qppd/smart-road-alert/ml/results/runs/detect/val/val_batch1_pred.jpg

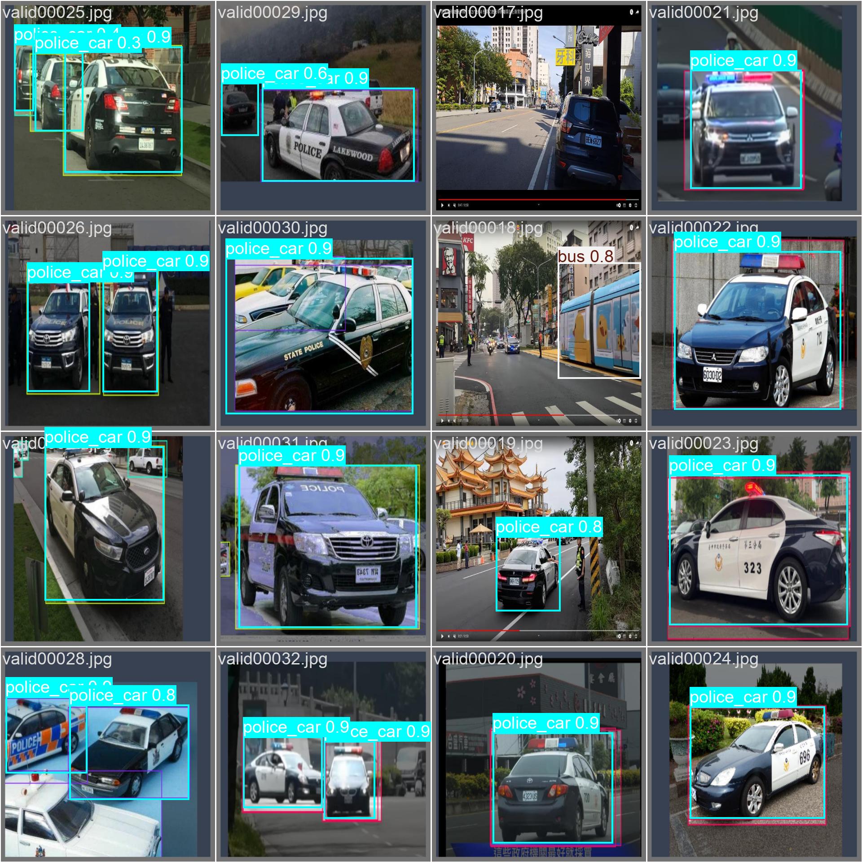
ml/results/runs/detect/val/val_batch1_pred.jpg
