qppd/smart-road-alert/ml/results/thesis_v3_results/g17_v3_final/val_batch2_pred.jpg

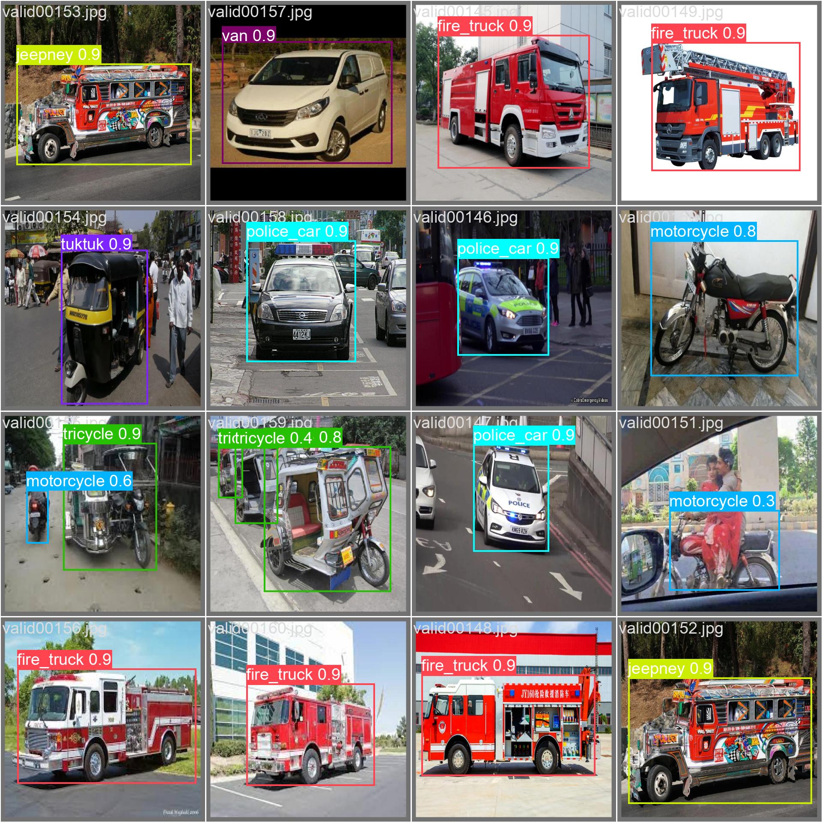
ml/results/thesis_v3_results/g17_v3_final/val_batch2_pred.jpg
