qppd/smart-road-alert/src/rpi/SmartRoadAlertHost/images/ambulance.jpg

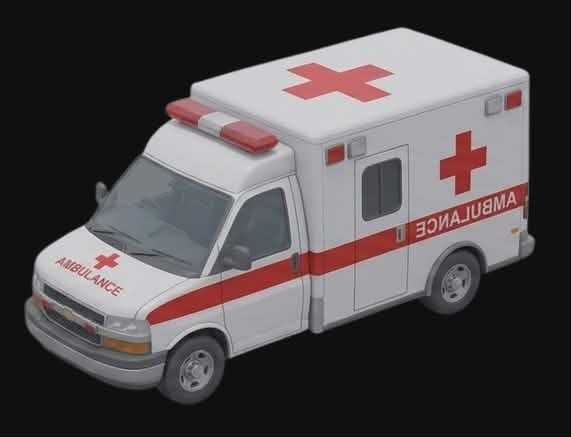
src/rpi/SmartRoadAlertHost/images/ambulance.jpg
