qppd/smart-road-alert/src/rpi/SmartRoadAlertHost/images/car.jpg

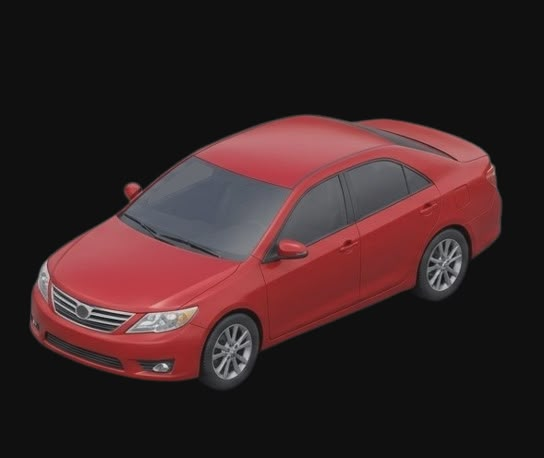
src/rpi/SmartRoadAlertHost/images/car.jpg
