qppd/smart-road-alert/src/rpi/SmartRoadAlertHost/images/ev_small.jpg

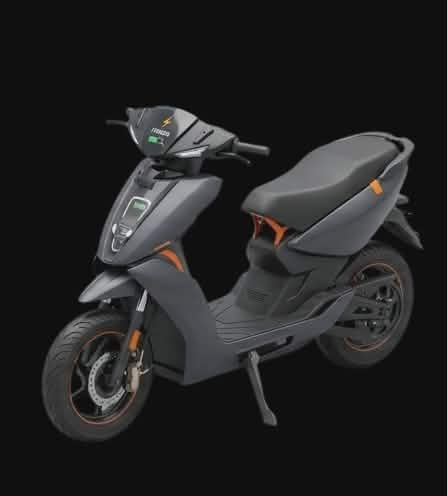
src/rpi/SmartRoadAlertHost/images/ev_small.jpg
