qppd/smart-road-alert/src/rpi/SmartRoadAlertHost/images/kariton.jpg

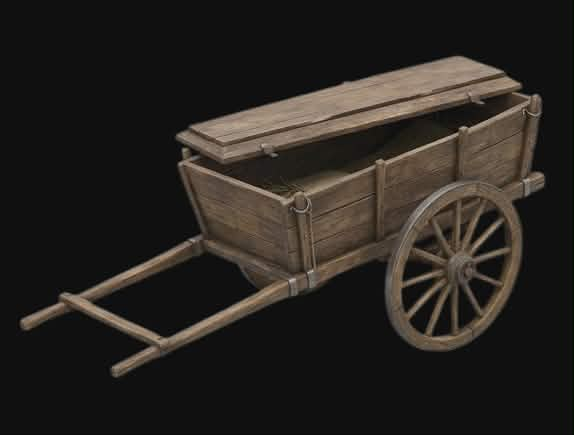
src/rpi/SmartRoadAlertHost/images/kariton.jpg
