qppd/smart-road-alert/src/rpi/SmartRoadAlertHost/images/pedicab.jpg

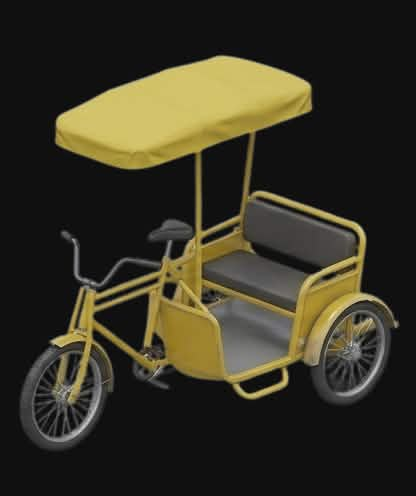
src/rpi/SmartRoadAlertHost/images/pedicab.jpg
