qppd/smart-road-alert/src/rpi/SmartRoadAlertHost/images/police_car.jpg

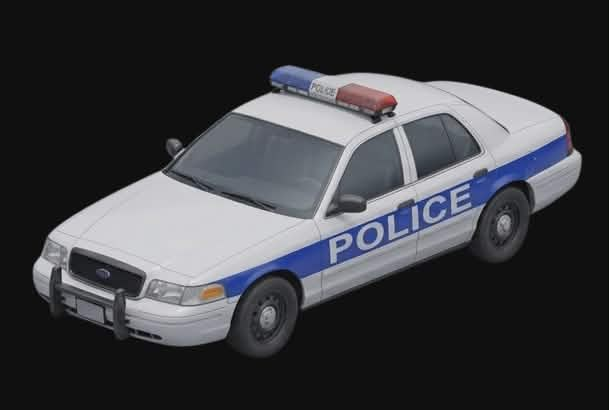
src/rpi/SmartRoadAlertHost/images/police_car.jpg
