qppd/smart-road-alert/src/rpi/SmartRoadAlertHost/images/tricycle.jpg

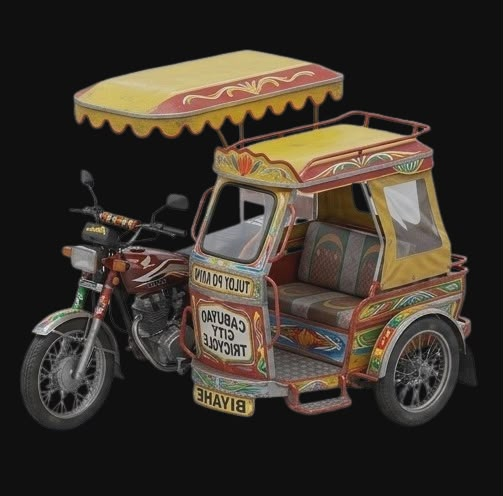
src/rpi/SmartRoadAlertHost/images/tricycle.jpg
