qppd/smart-road-alert/src/rpi/SmartRoadAlertHost/images/truck.jpg

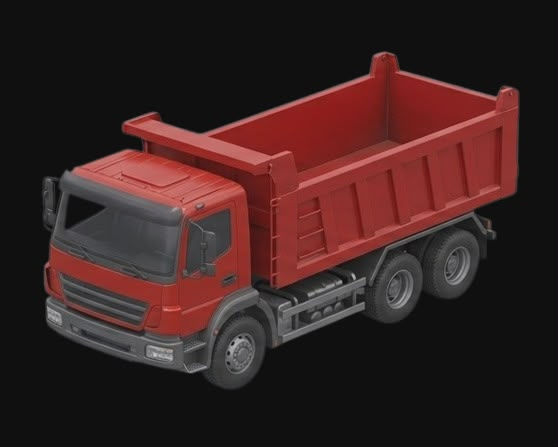
src/rpi/SmartRoadAlertHost/images/truck.jpg
