qppd/smart-road-alert/src/rpi/SmartRoadAlertHost/images/tuktuk.jpg

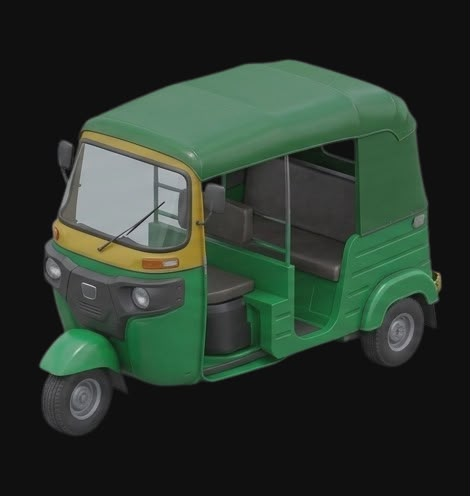
src/rpi/SmartRoadAlertHost/images/tuktuk.jpg
