qppd/smart-road-alert/src/rpi/SmartRoadAlertHost/images/van.jpg

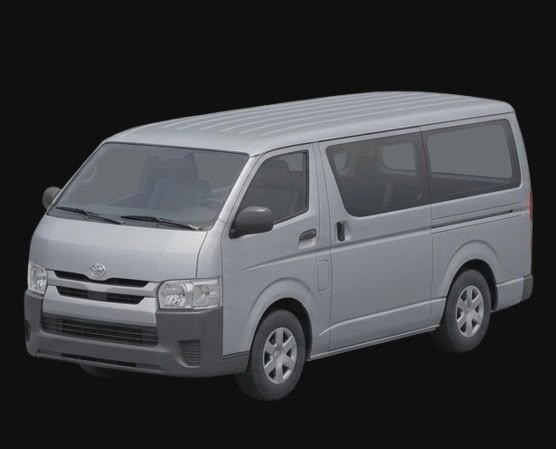
src/rpi/SmartRoadAlertHost/images/van.jpg
