qppd/smart-road-alert/ml/results/runs/detect/val/BoxF1_curve.png

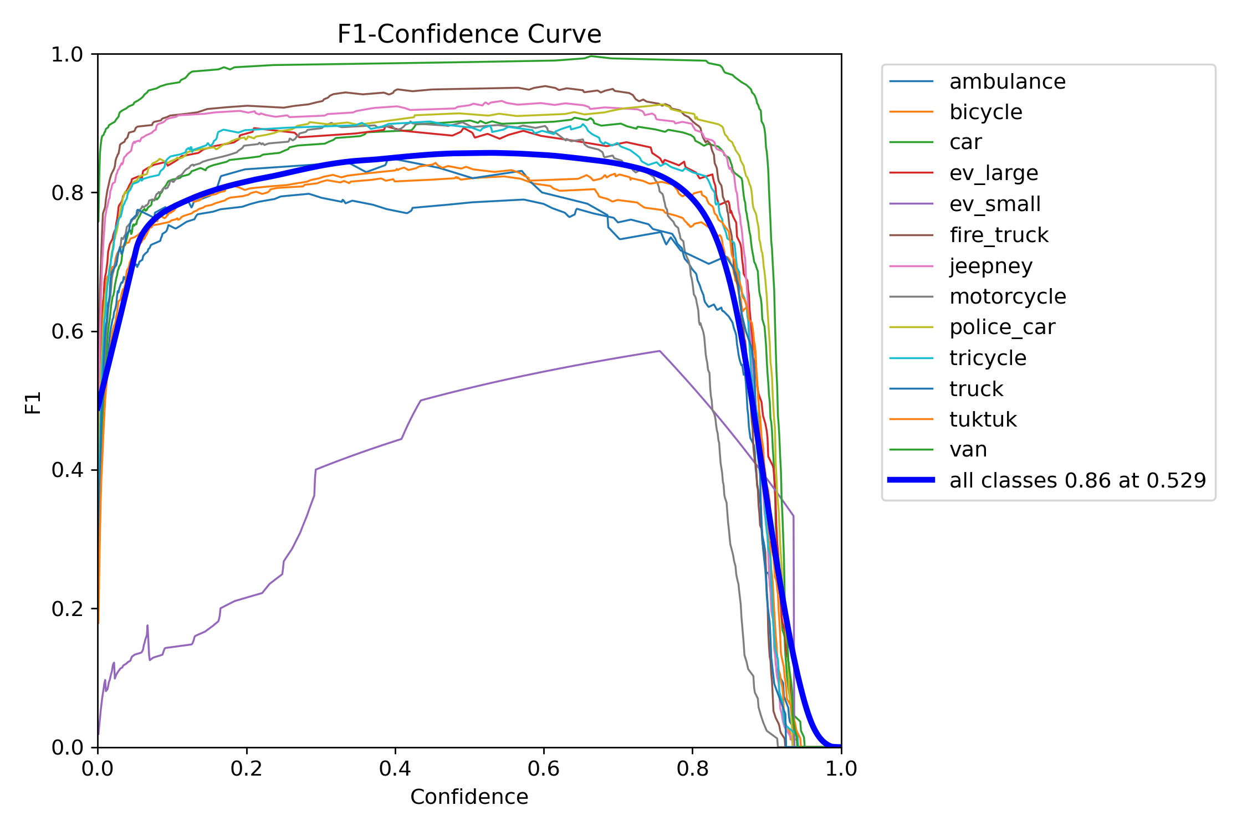
ml/results/runs/detect/val/BoxF1_curve.png
