qppd/smart-road-alert/ml/results/runs/detect/val/BoxP_curve.png

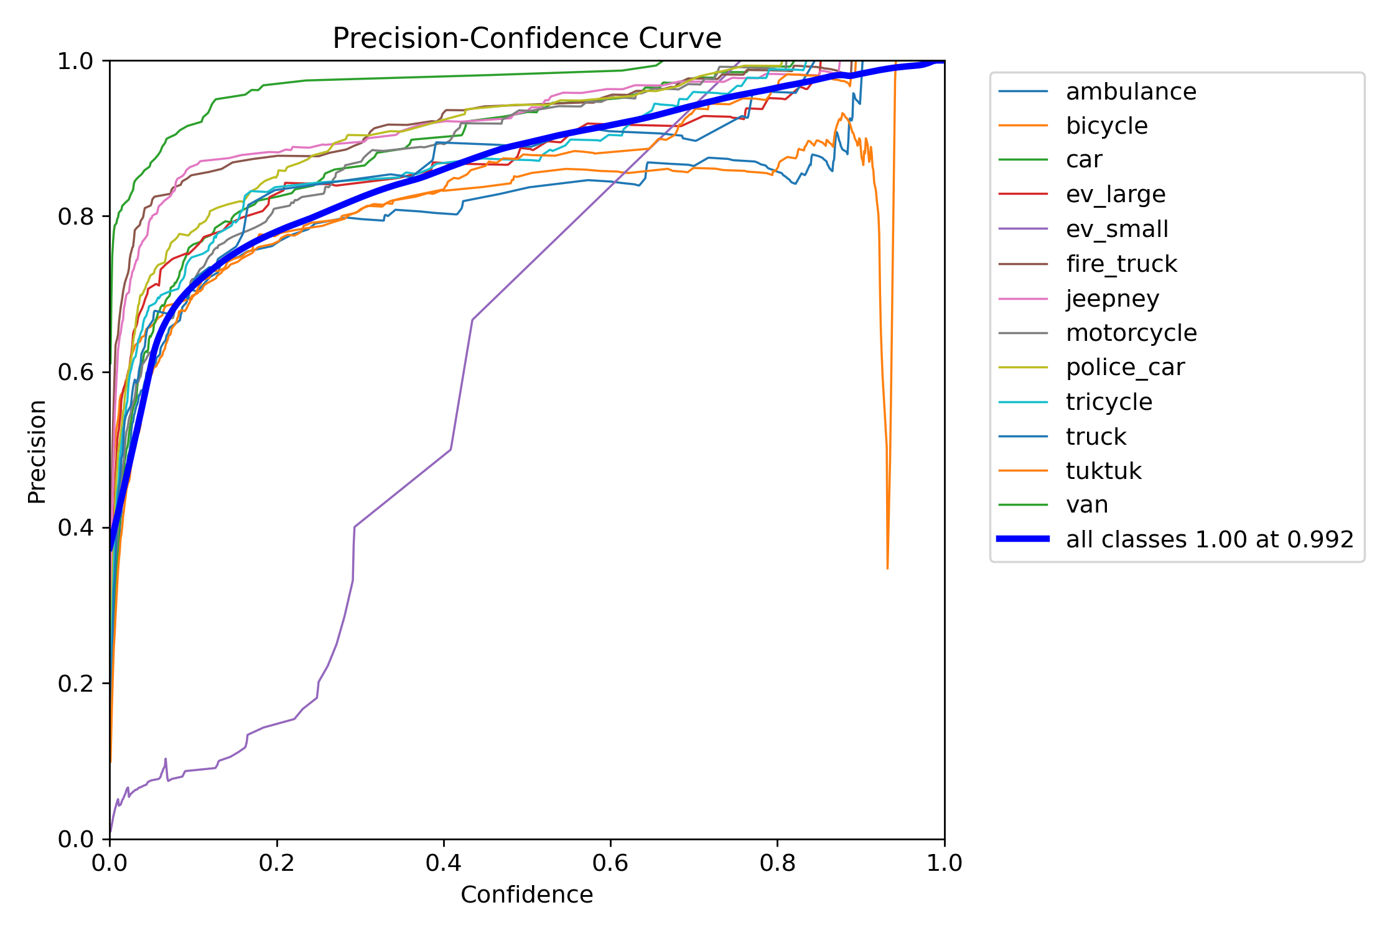
ml/results/runs/detect/val/BoxP_curve.png
