qppd/smart-road-alert/ml/results/runs/detect/val/BoxPR_curve.png

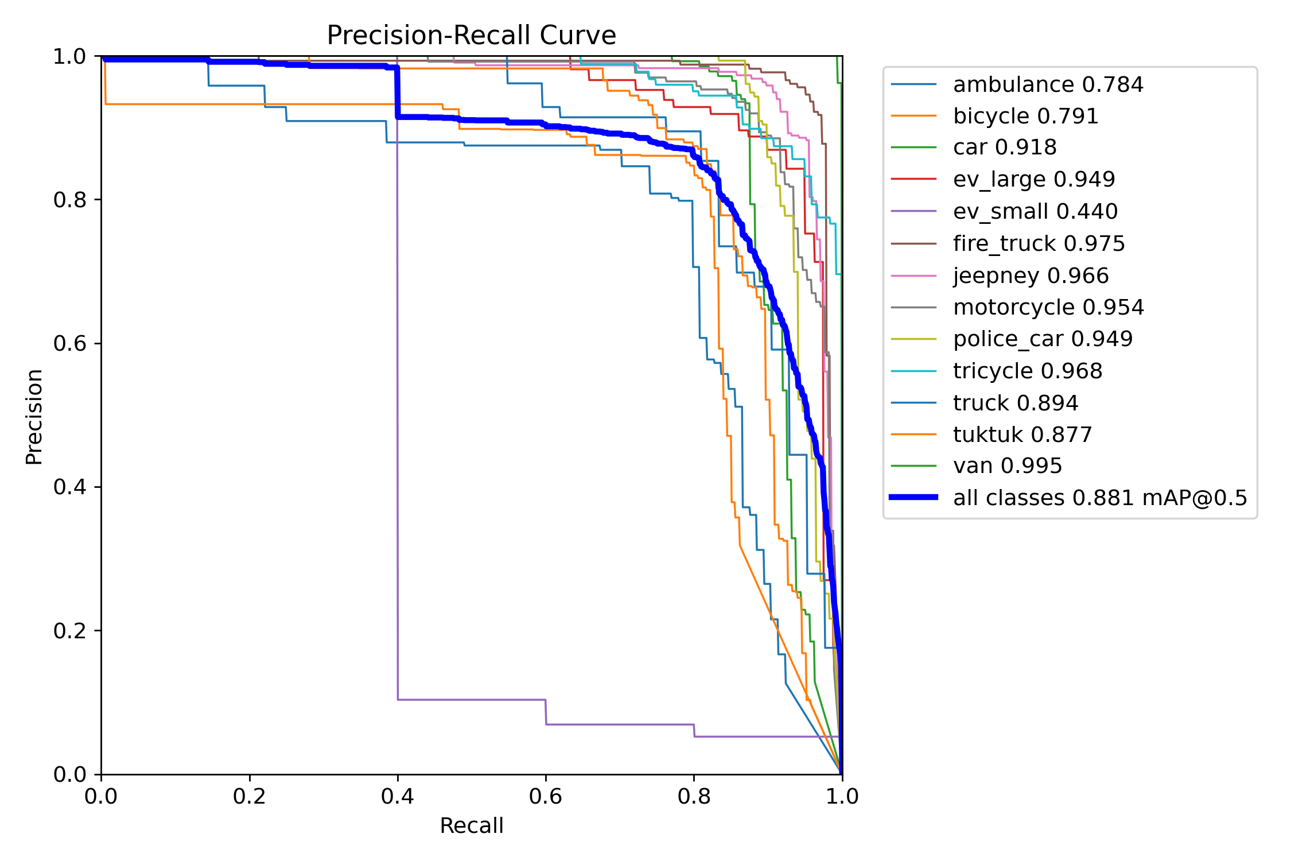
ml/results/runs/detect/val/BoxPR_curve.png
