qppd/smart-road-alert/ml/results/runs/detect/val/BoxR_curve.png

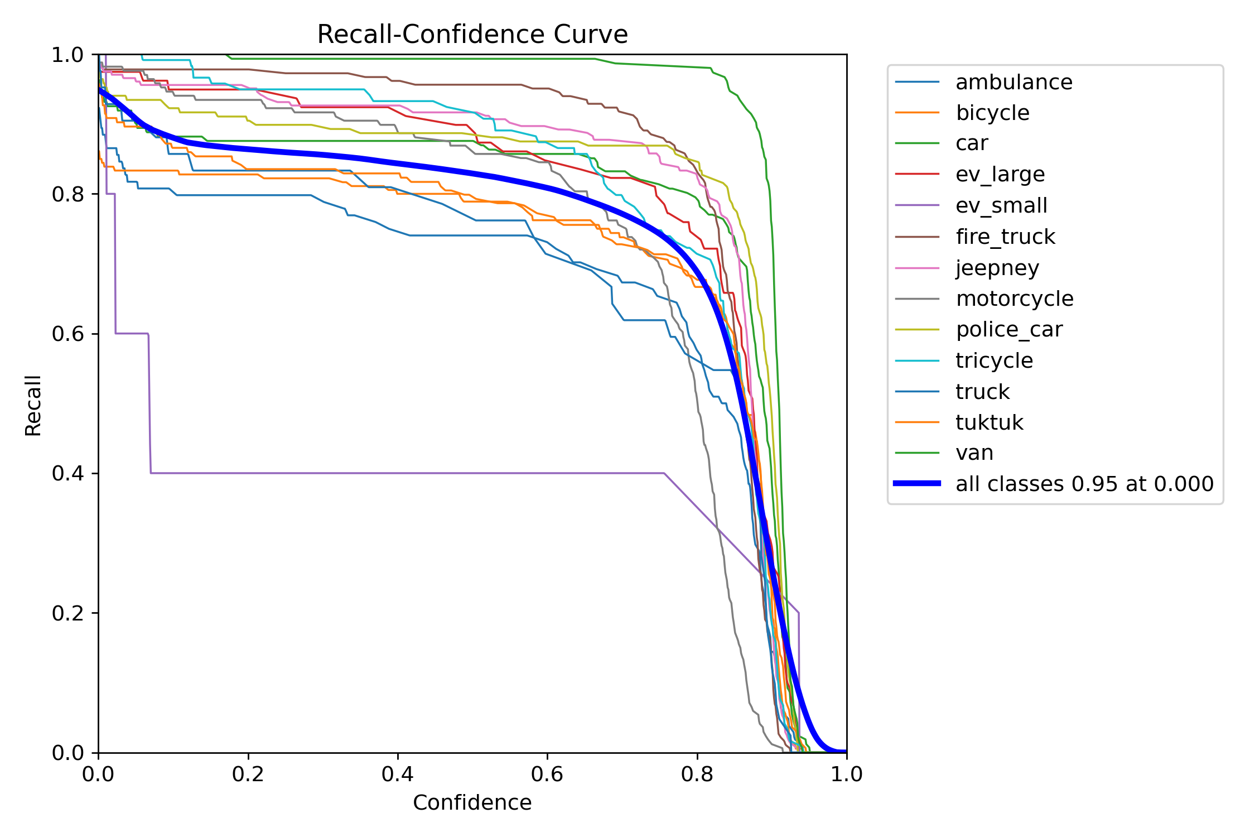
ml/results/runs/detect/val/BoxR_curve.png
