qppd/smart-road-alert/ml/results/runs/detect/val/confusion_matrix.png

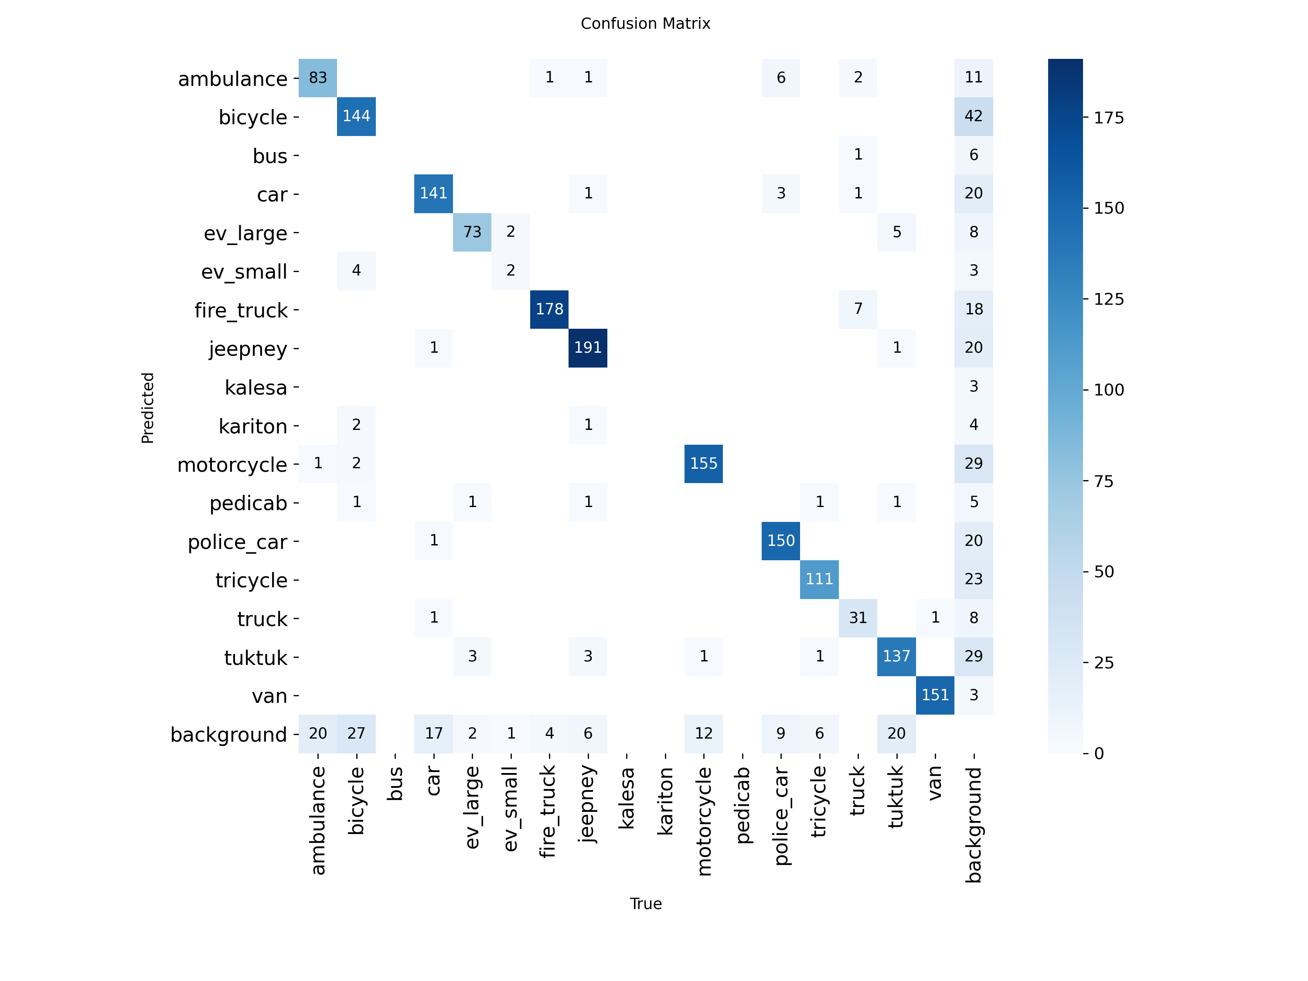
ml/results/runs/detect/val/confusion_matrix.png
