qppd/smart-road-alert/ml/results/runs/detect/val/confusion_matrix_normalized.png

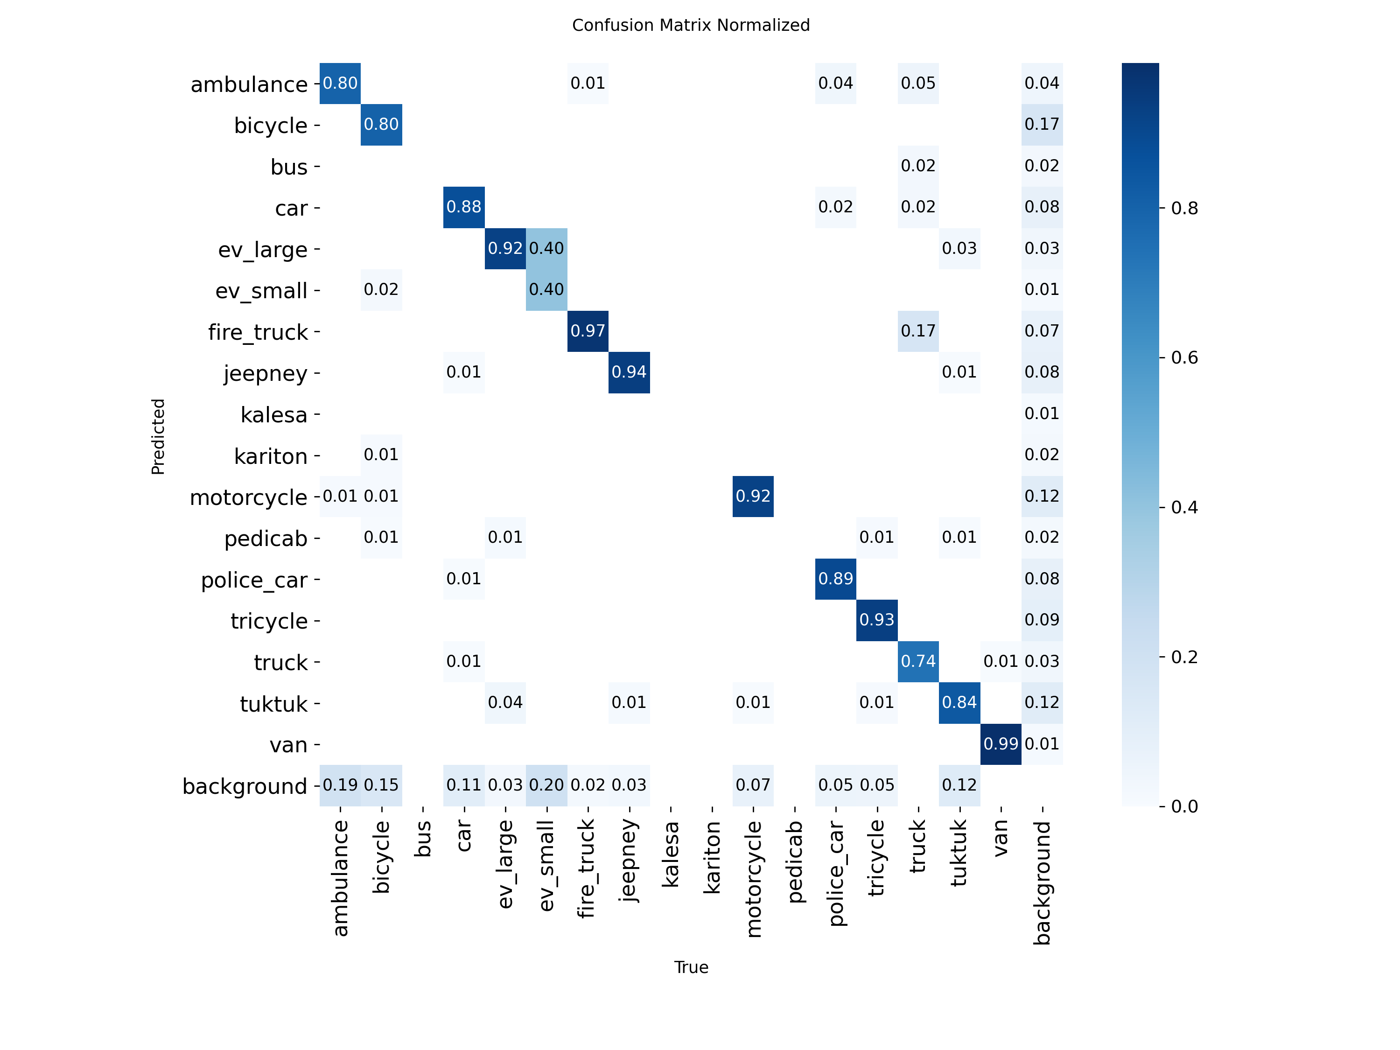
ml/results/runs/detect/val/confusion_matrix_normalized.png
