qppd/smart-road-alert/ml/results/runs/detect/val/val_batch0_labels.jpg

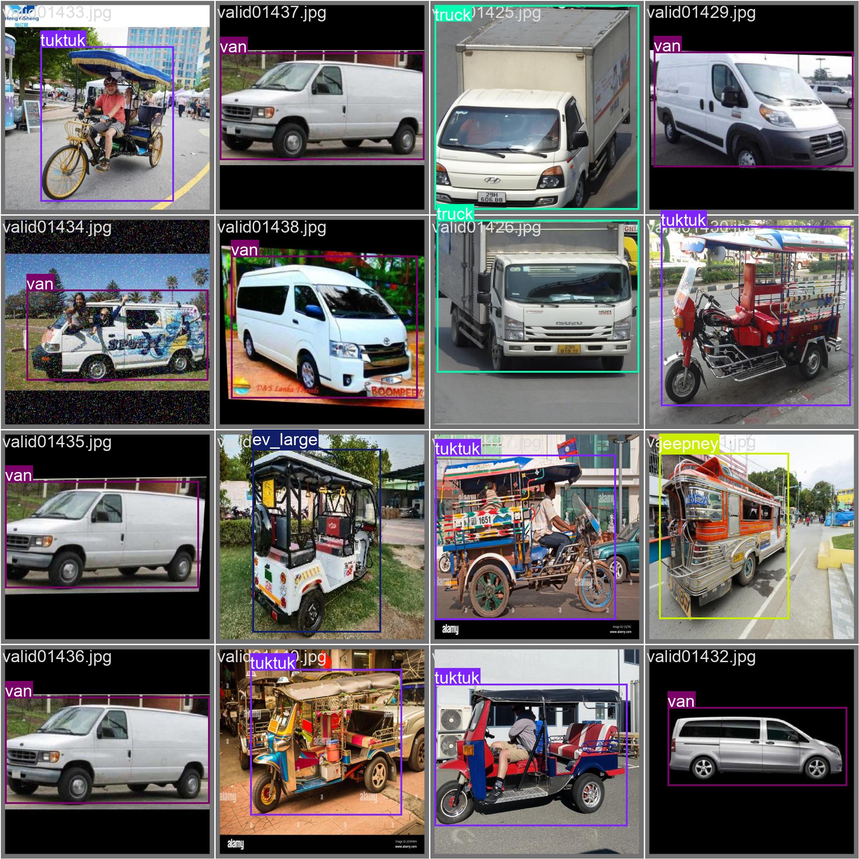
ml/results/runs/detect/val/val_batch0_labels.jpg
