qppd/smart-road-alert/ml/results/runs/detect/val/val_batch2_labels.jpg

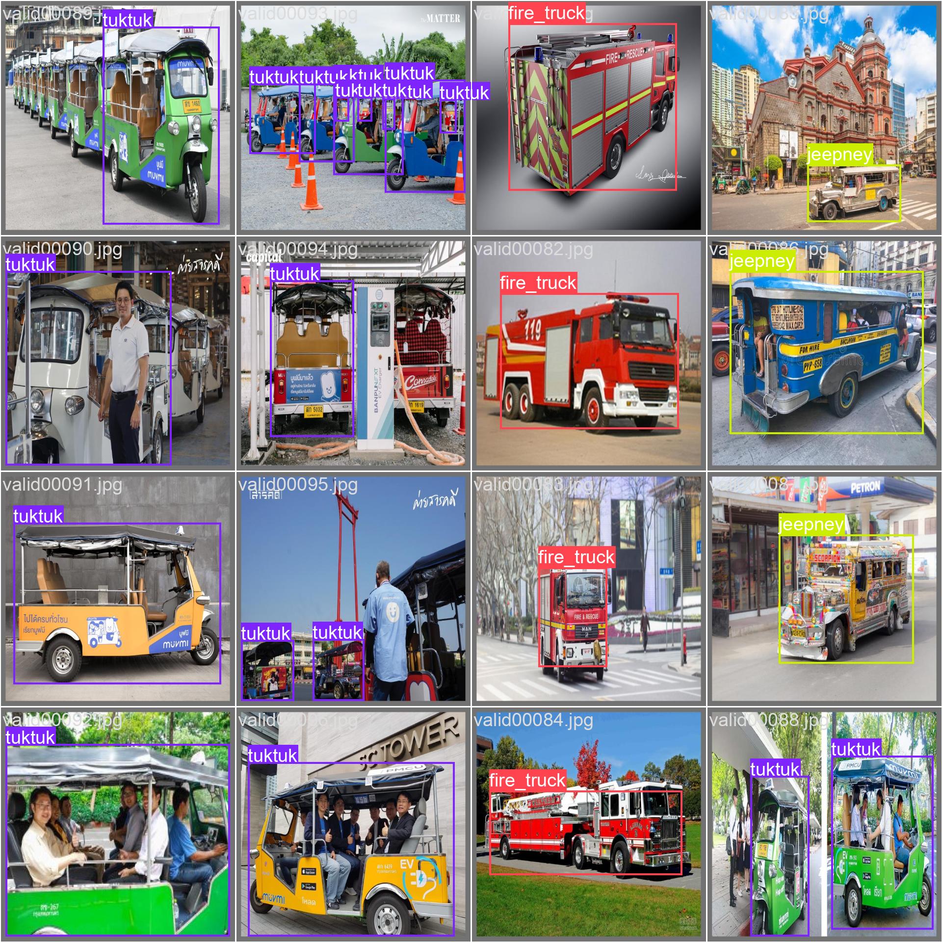
ml/results/runs/detect/val/val_batch2_labels.jpg
