qppd/smart-road-alert/ml/results/thesis_v3_results/custom_plots/00_class_distribution.png

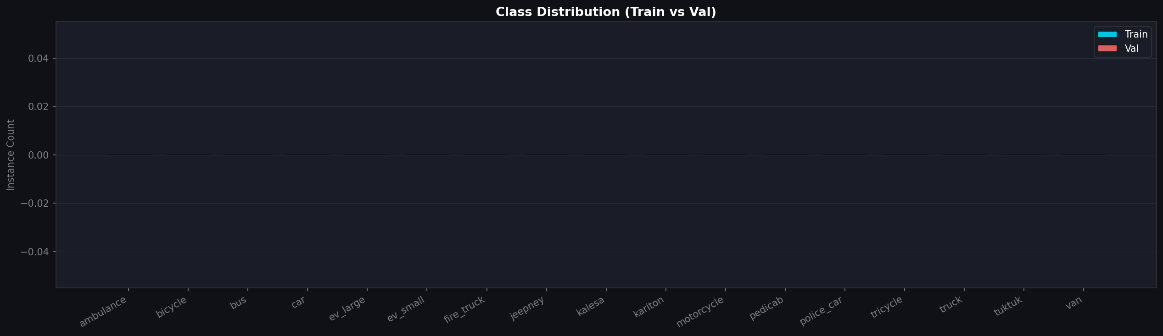
ml/results/thesis_v3_results/custom_plots/00_class_distribution.png
