qppd/smart-road-alert/ml/results/thesis_v3_results/custom_plots/01_training_curves.png

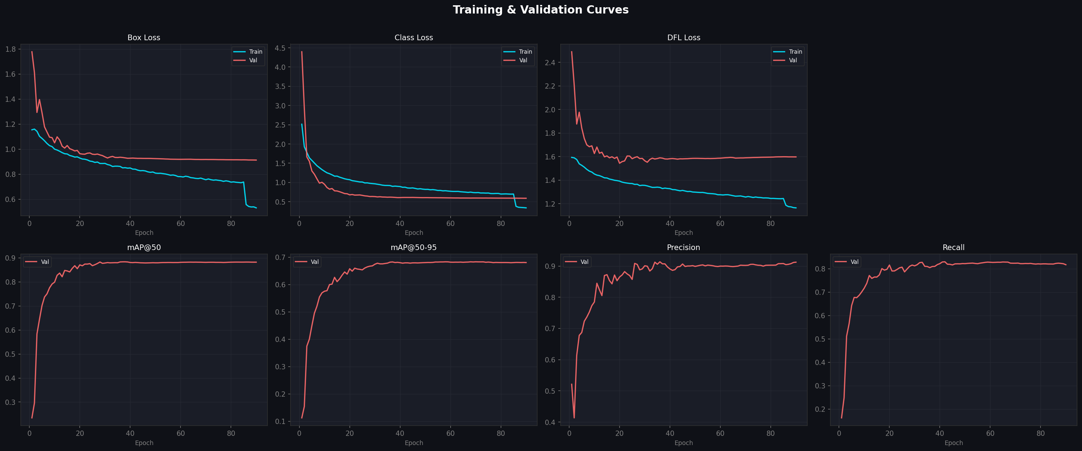
ml/results/thesis_v3_results/custom_plots/01_training_curves.png
