qppd/smart-road-alert/ml/results/thesis_v3_results/custom_plots/02_lr_schedule.png

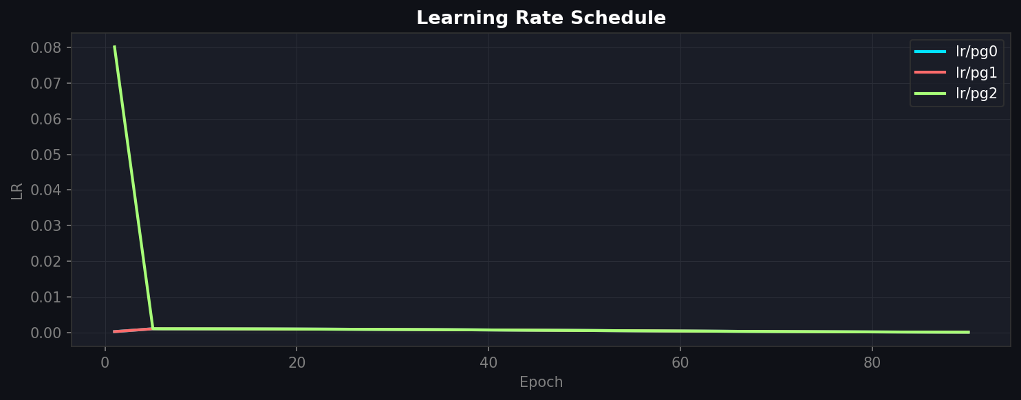
ml/results/thesis_v3_results/custom_plots/02_lr_schedule.png
