qppd/smart-road-alert/ml/results/thesis_v3_results/custom_plots/05_performance_radar.png

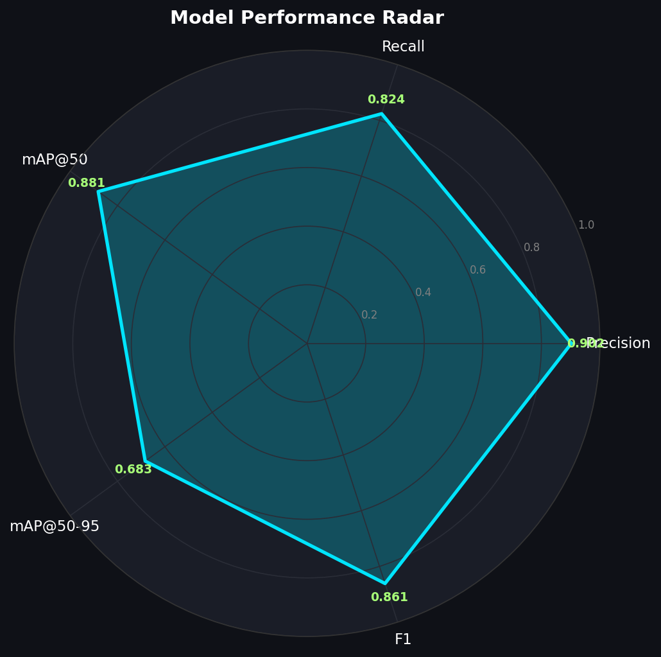
ml/results/thesis_v3_results/custom_plots/05_performance_radar.png
