qppd/smart-road-alert/ml/results/thesis_v3_results/g17_v3_final/train_batch0.jpg

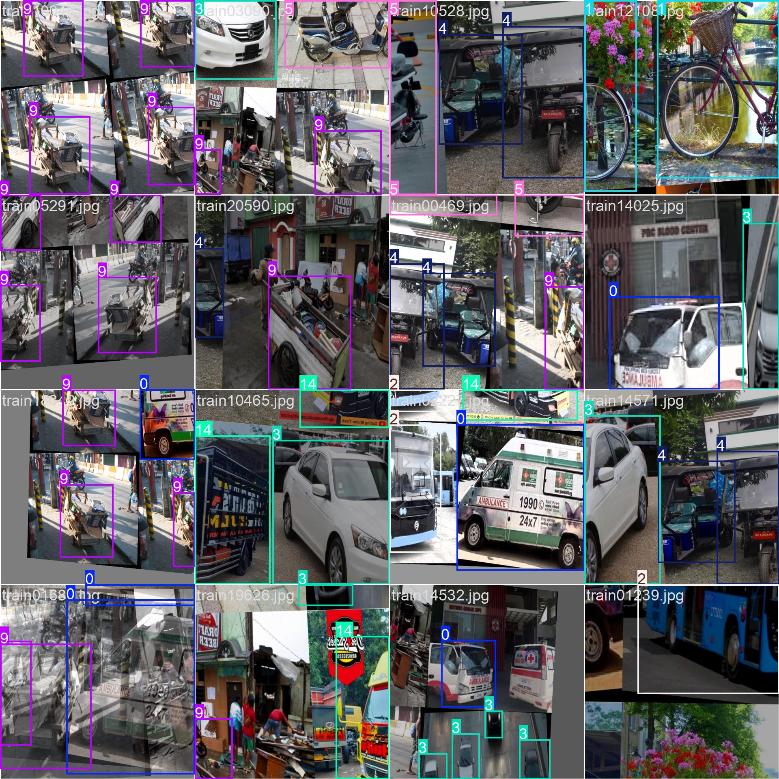
ml/results/thesis_v3_results/g17_v3_final/train_batch0.jpg
