qppd/smart-road-alert/ml/results/thesis_v3_results/g17_v3_final_test/BoxF1_curve.png

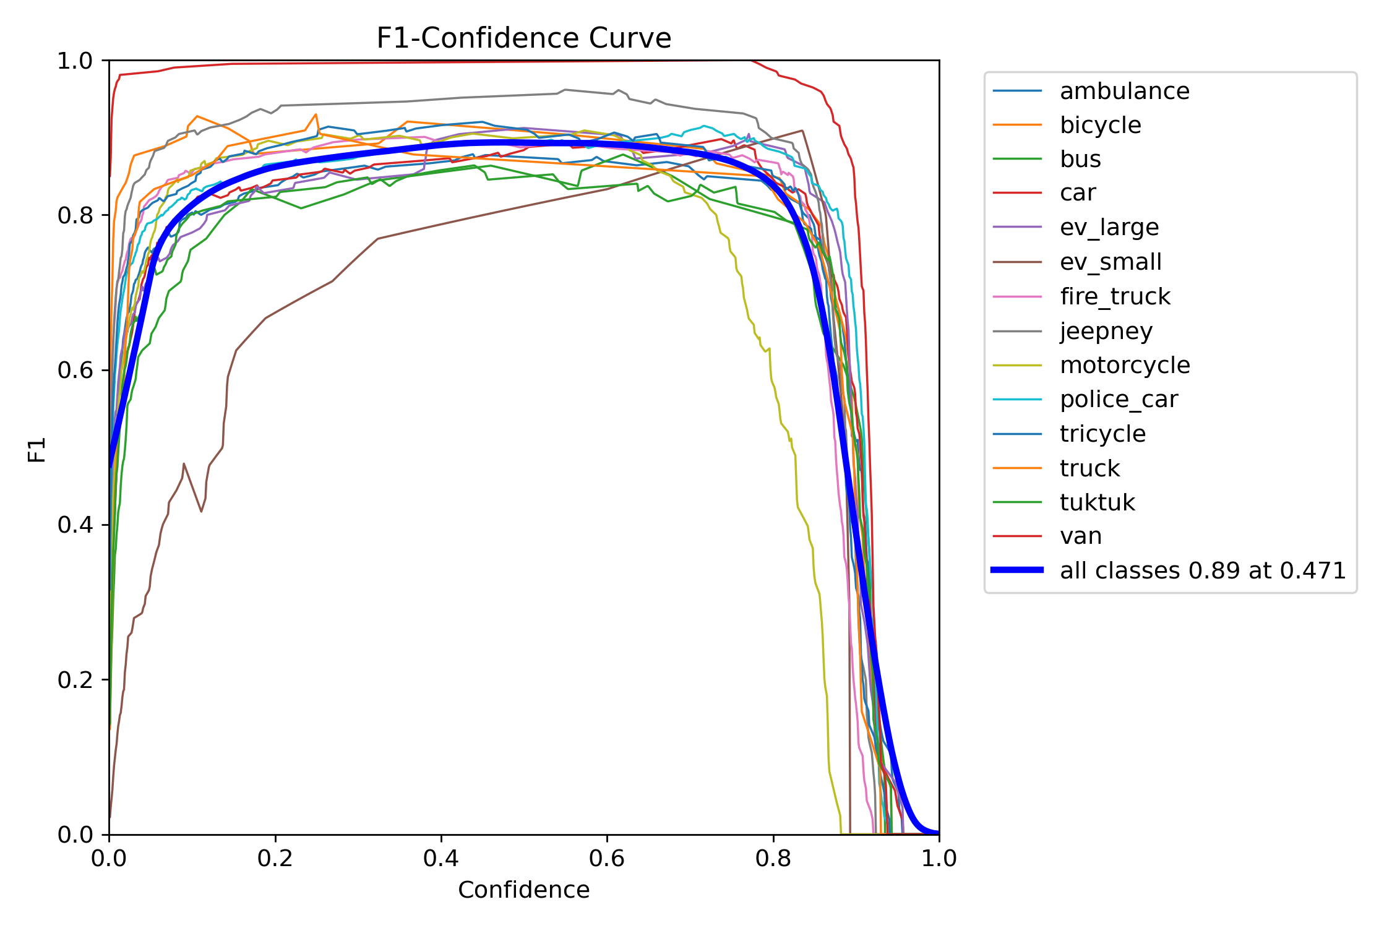
ml/results/thesis_v3_results/g17_v3_final_test/BoxF1_curve.png
