qppd/smart-road-alert/ml/results/thesis_v3_results/g17_v3_final_test/BoxR_curve.png

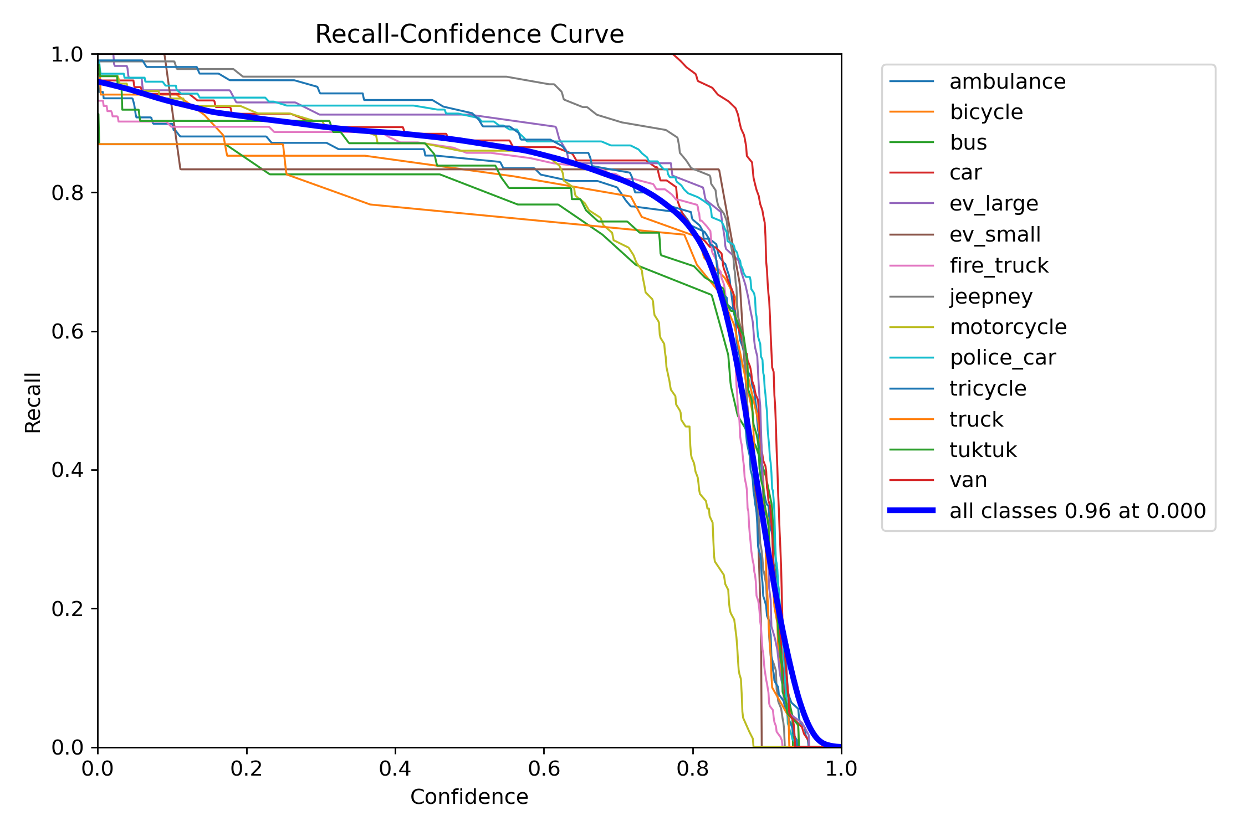
ml/results/thesis_v3_results/g17_v3_final_test/BoxR_curve.png
