qppd/smart-road-alert/ml/results/thesis_v3_results/g17_v3_final_test/val_batch0_labels.jpg

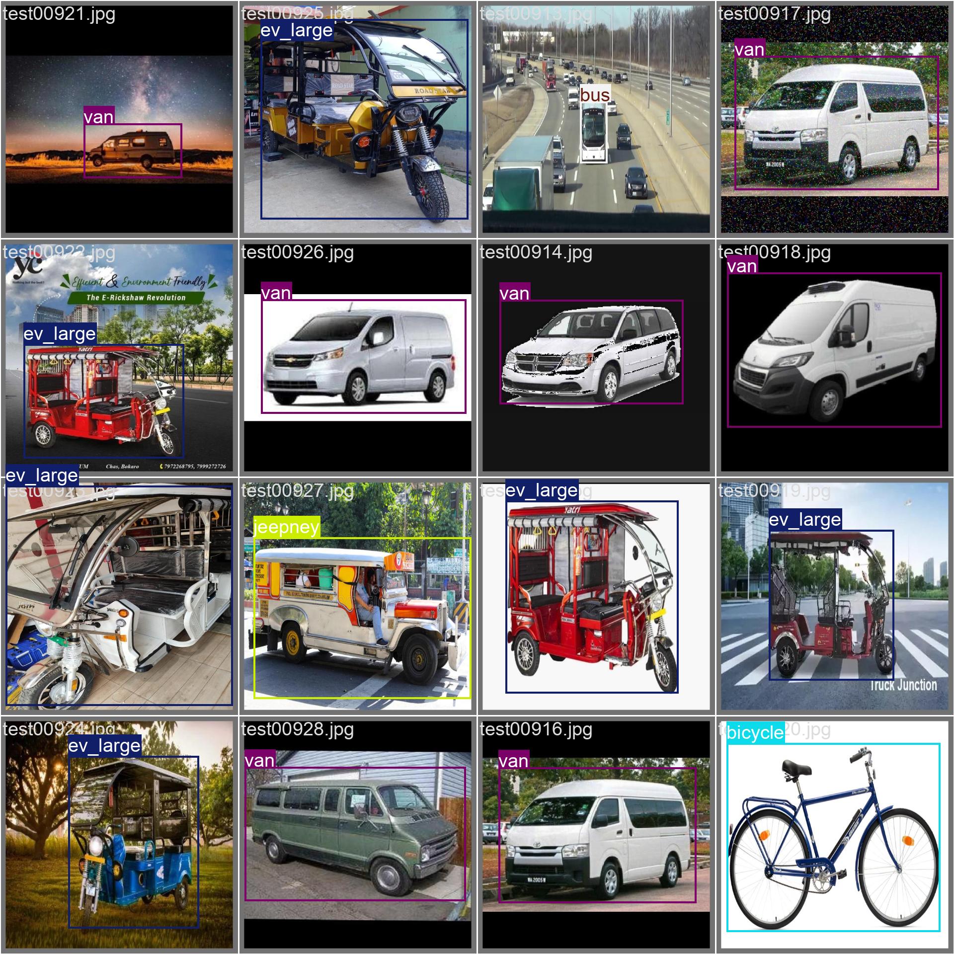
ml/results/thesis_v3_results/g17_v3_final_test/val_batch0_labels.jpg
